DianaNigrisoli/Handy_SensorizedGlove/Software/01_Graphics/hearthands.jpg

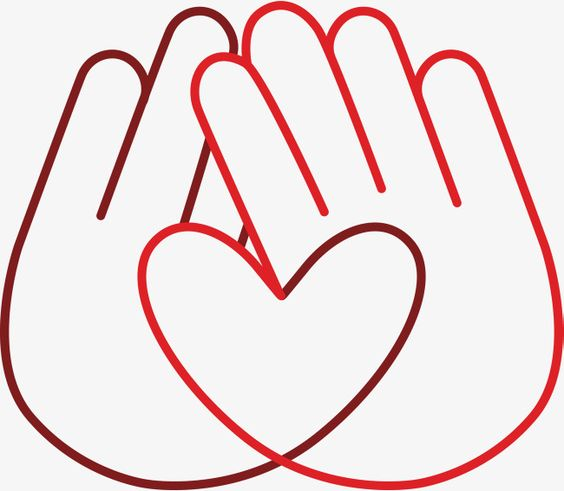
Software/01_Graphics/hearthands.jpg
