DianaNigrisoli/Handy_SensorizedGlove/Software/01_Graphics/download.jpeg

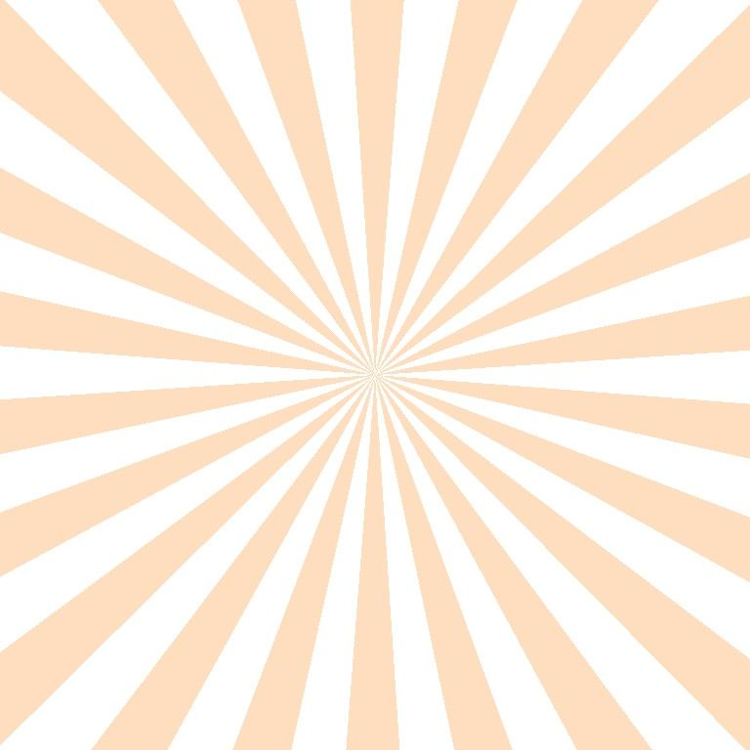
Software/01_Graphics/download.jpeg
