DianaNigrisoli/Handy_SensorizedGlove/Software/01_Graphics/hands.jpg

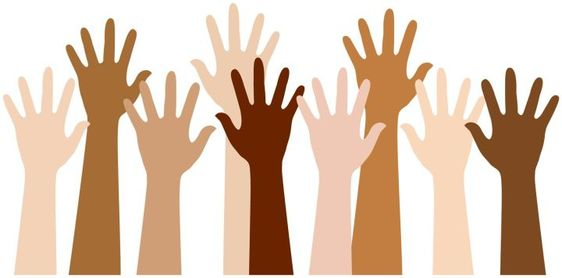
Software/01_Graphics/hands.jpg
