DianaNigrisoli/Handy_SensorizedGlove/Software/01_Graphics/Immagine carina ASL.jpg

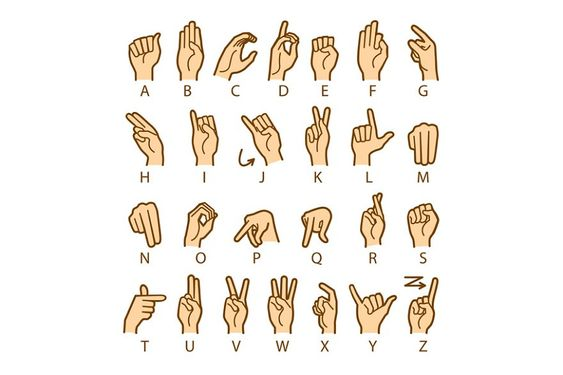
Software/01_Graphics/Immagine carina ASL.jpg
